peej/lumberjack-keyboard/images/tofu-sa-vilebloom.jpg

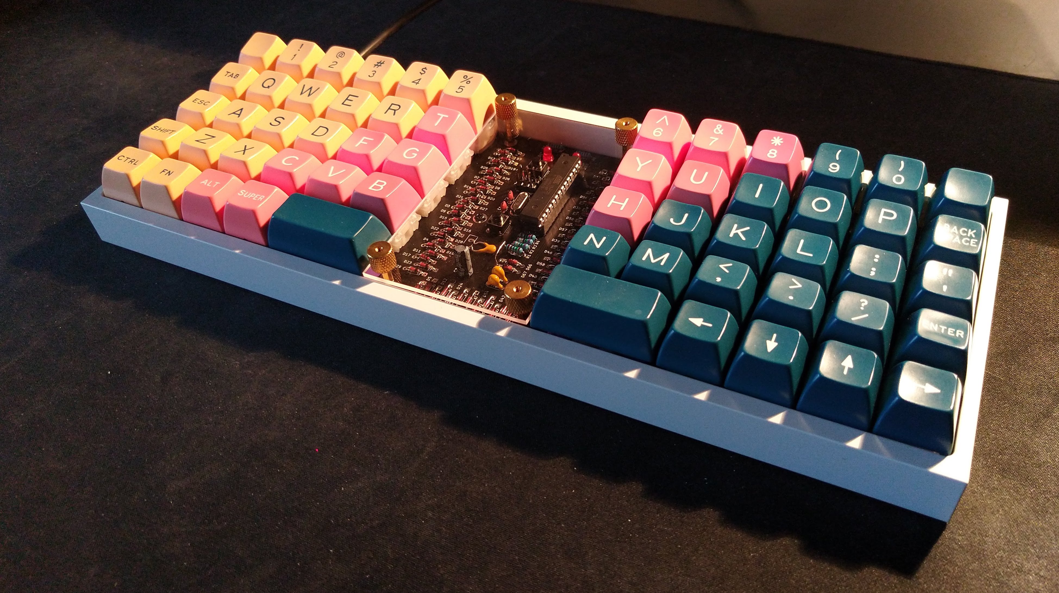
images/tofu-sa-vilebloom.jpg
