peej/lumberjack-keyboard/images/bom/j1-mini.jpg

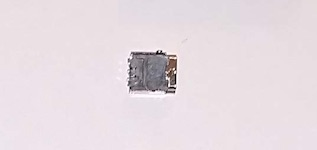
images/bom/j1-mini.jpg
