peej/lumberjack-keyboard/plates/lumberjack-split.dxf

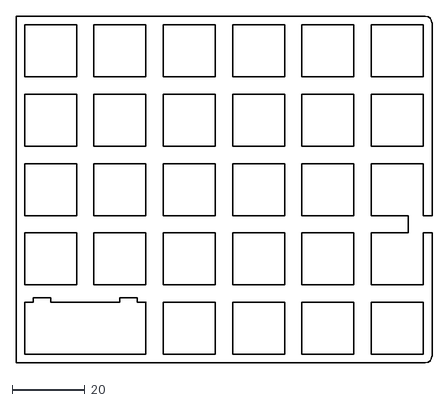
[picture p46: CAD file, 2021-04-14]
plates/lumberjack-split.dxf
114.3 x 95.2
