peej/lumberjack-keyboard/images/guide/usb-c.jpg

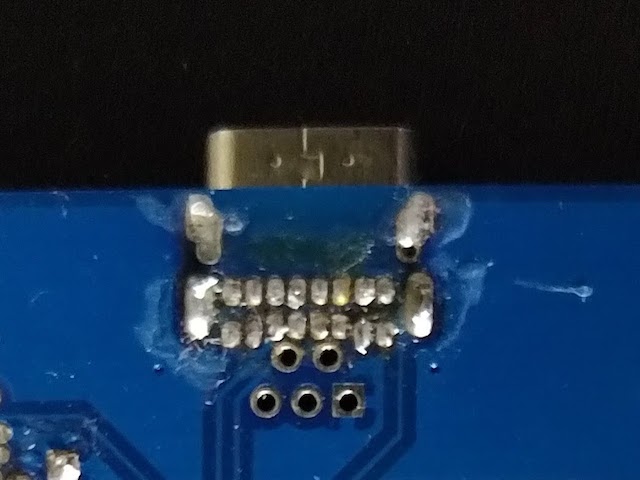
images/guide/usb-c.jpg
