peej/lumberjack-keyboard/images/guide/usb_underside.jpg

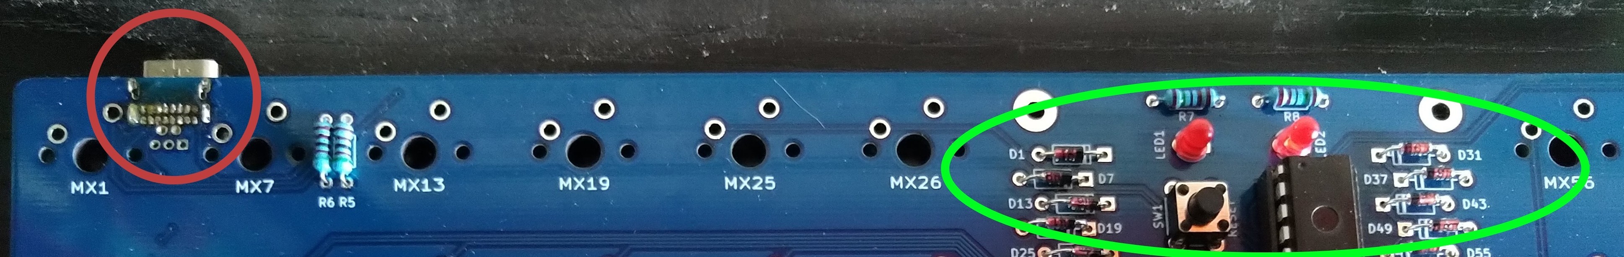
images/guide/usb_underside.jpg
